markday275/RoboCup/CAD/InductiveProxSensor.SLDPRT

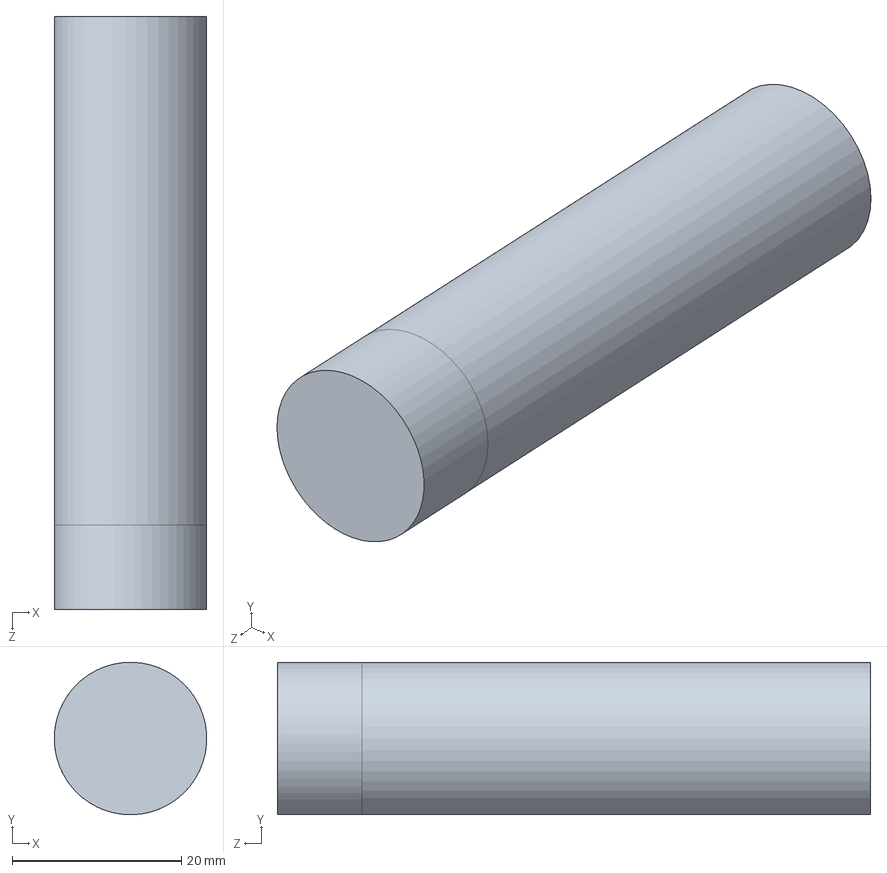
[picture p46: CAD file, 2024-11-14]
CAD/InductiveProxSensor.SLDPRT
18.0 x 18.0 x 70.0 mm
