markday275/RoboCup/CAD/Gate.SLDPRT

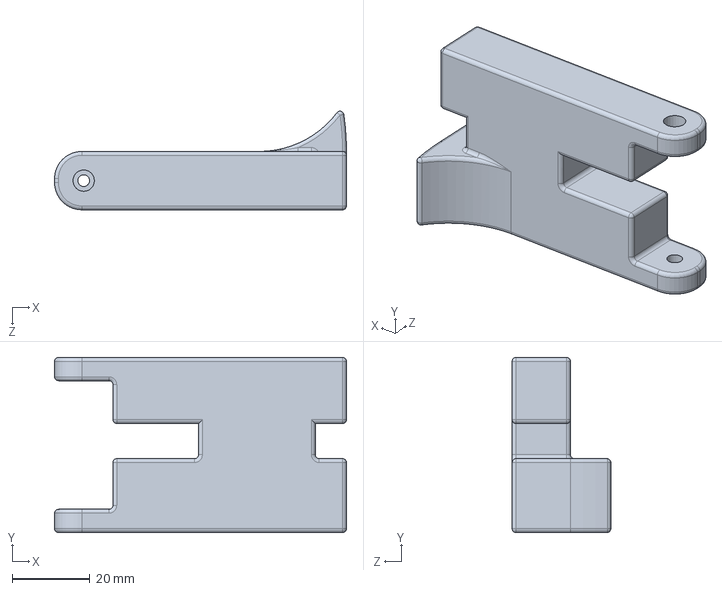
[picture p47: CAD file, 2024-11-14]
CAD/Gate.SLDPRT
75.0 x 45.0 x 25.3 mm
