markday275/RoboCup/CAD/RH Tray Back.SLDPRT

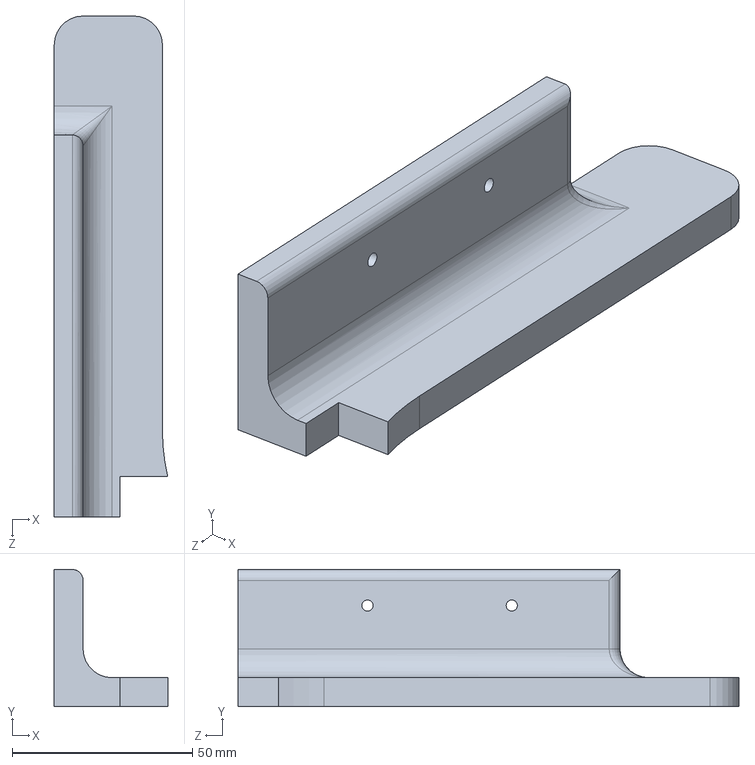
[picture p48: CAD file, 2024-11-14]
CAD/RH Tray Back.SLDPRT
31.5 x 38.0 x 138.9 mm
