markday275/RoboCup/CAD/RH Tray Front.SLDPRT

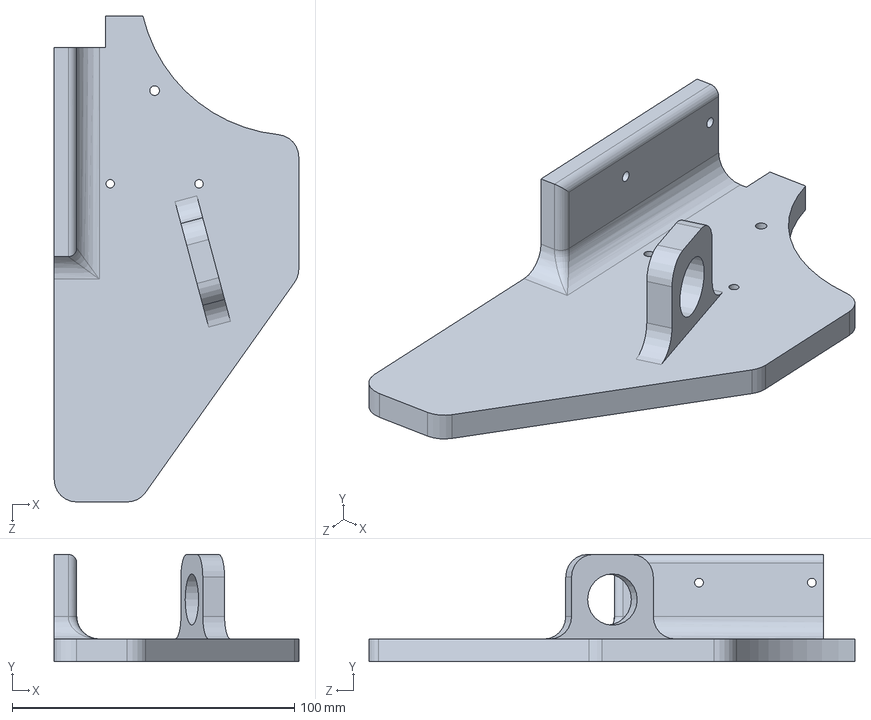
[picture p49: CAD file, 2024-11-14]
CAD/RH Tray Front.SLDPRT
86.8 x 38.0 x 172.3 mm
