markday275/RoboCup/CAD/digitalBoardBracket.SLDPRT

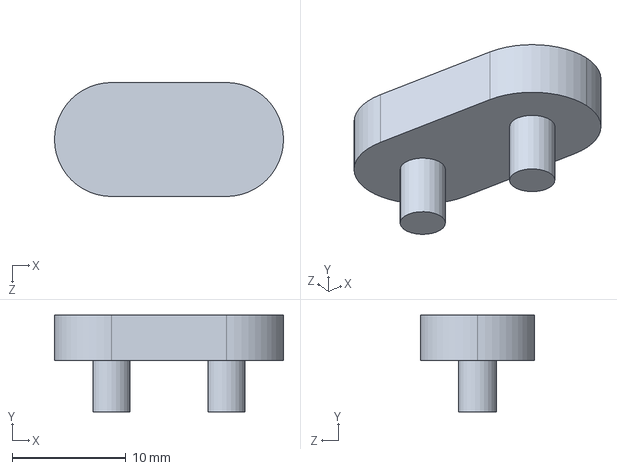
[picture p50: CAD file, 2024-11-14]
CAD/digitalBoardBracket.SLDPRT
20.1 x 8.50 x 10.0 mm
