markday275/RoboCup/CAD/ColourSensor.SLDPRT

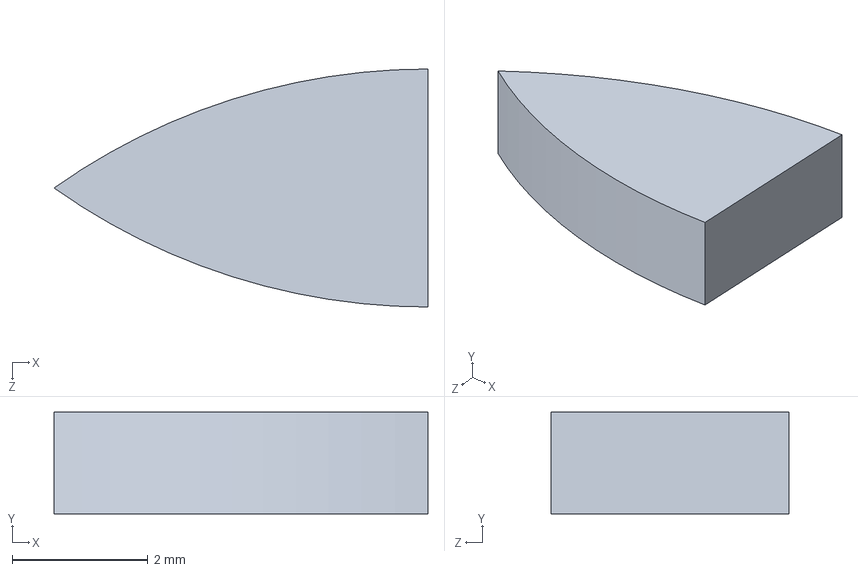
[picture p51: CAD file, 2024-11-14]
CAD/ColourSensor.SLDPRT
5.50 x 1.50 x 3.50 mm
