markday275/RoboCup/CAD/Partition.SLDPRT

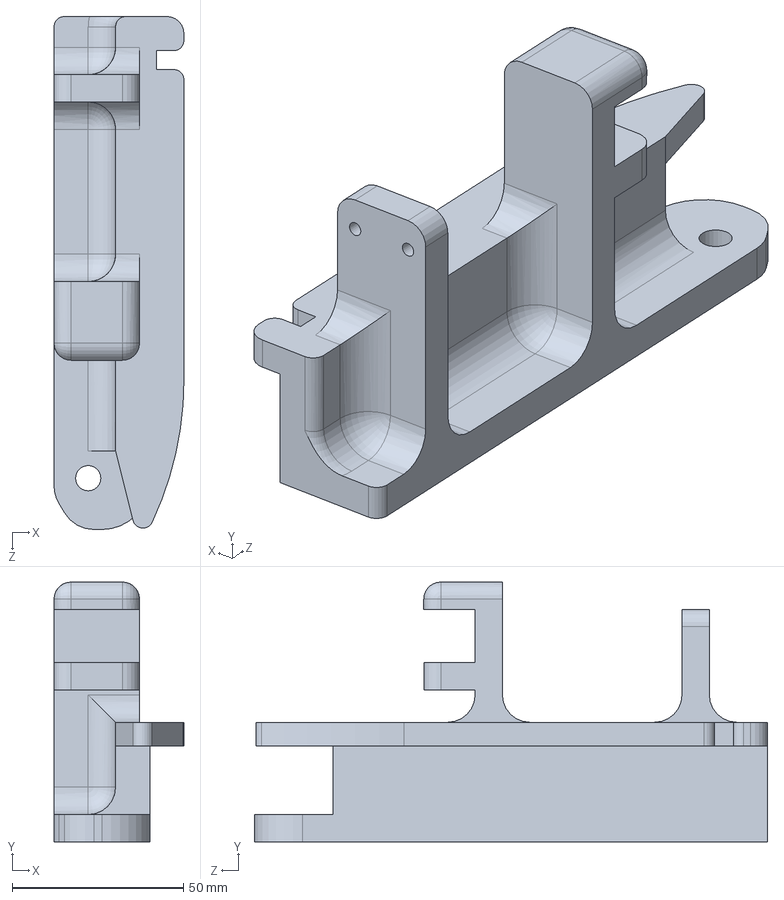
[picture p52: CAD file, 2024-11-14]
CAD/Partition.SLDPRT
38.0 x 76.0 x 150.0 mm
