markday275/RoboCup/CAD/digitalBoardBracket2.SLDPRT

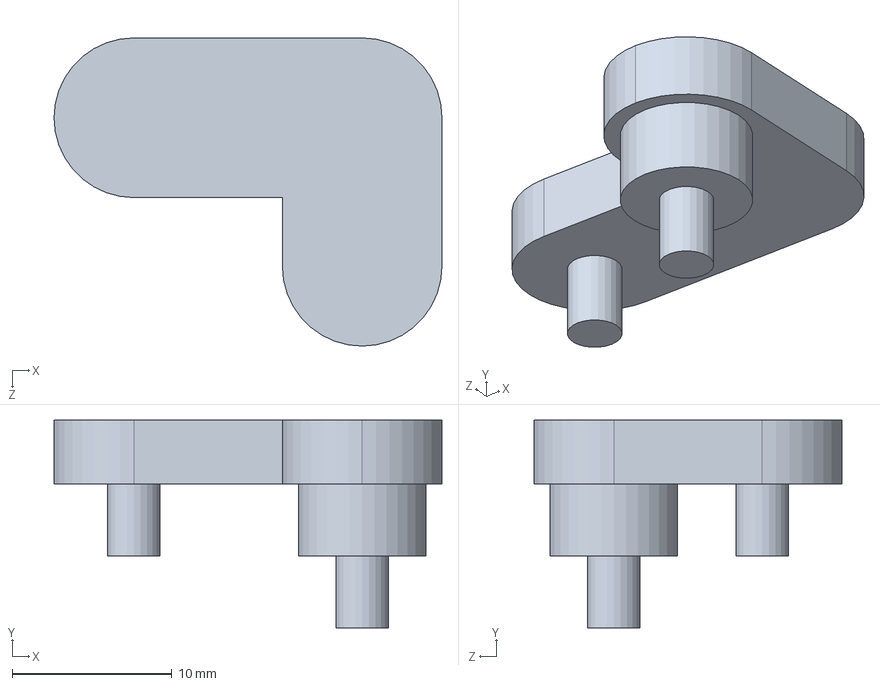
[picture p53: CAD file, 2024-11-14]
CAD/digitalBoardBracket2.SLDPRT
24.3 x 13.0 x 19.3 mm
