markday275/RoboCup/CAD/inductiveBoardBracket.SLDPRT

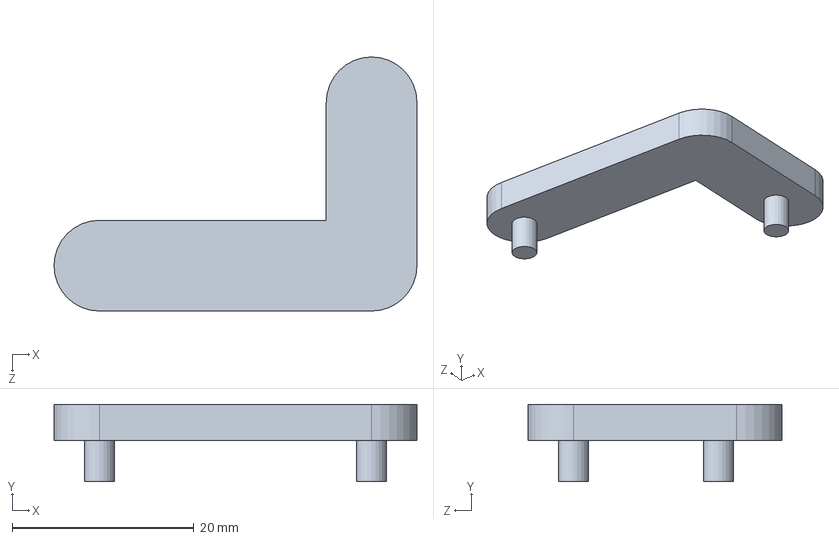
[picture p54: CAD file, 2024-11-14]
CAD/inductiveBoardBracket.SLDPRT
40.0 x 8.50 x 28.0 mm
