markday275/RoboCup/CAD/RH TRAY.SLDPRT

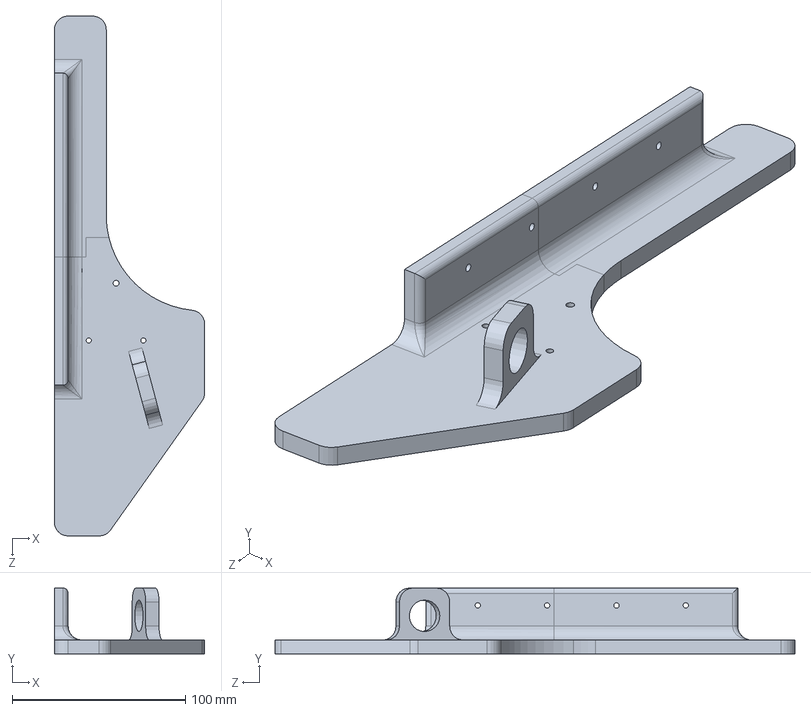
[picture p55: CAD file, 2024-11-14]
CAD/RH TRAY.SLDPRT
86.8 x 38.0 x 300.0 mm
