markday275/RoboCup/CAD/LH TRAY NEW SLOT.SLDPRT

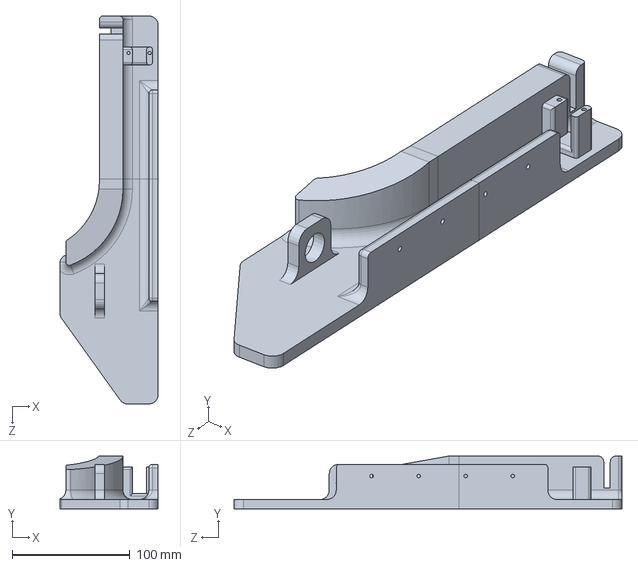
[picture p56: CAD file, 2024-11-14]
CAD/LH TRAY NEW SLOT.SLDPRT
83.8 x 45.0 x 330.0 mm
