markday275/RoboCup/CAD/LH TRAY.SLDPRT

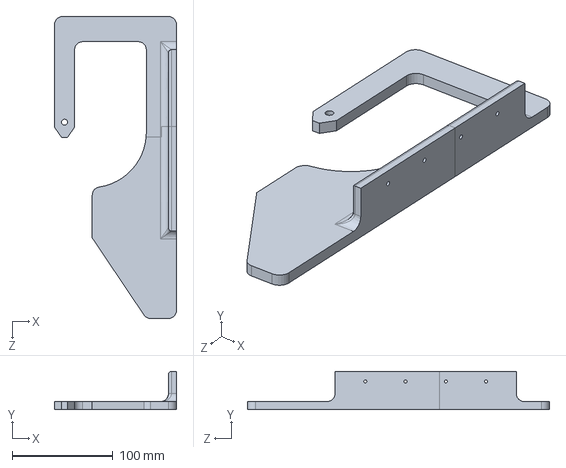
[picture p57: CAD file, 2024-11-14]
CAD/LH TRAY.SLDPRT
121.2 x 38.0 x 300.0 mm
