markday275/RoboCup/CAD/Digital_IR_Sensor.SLDPRT

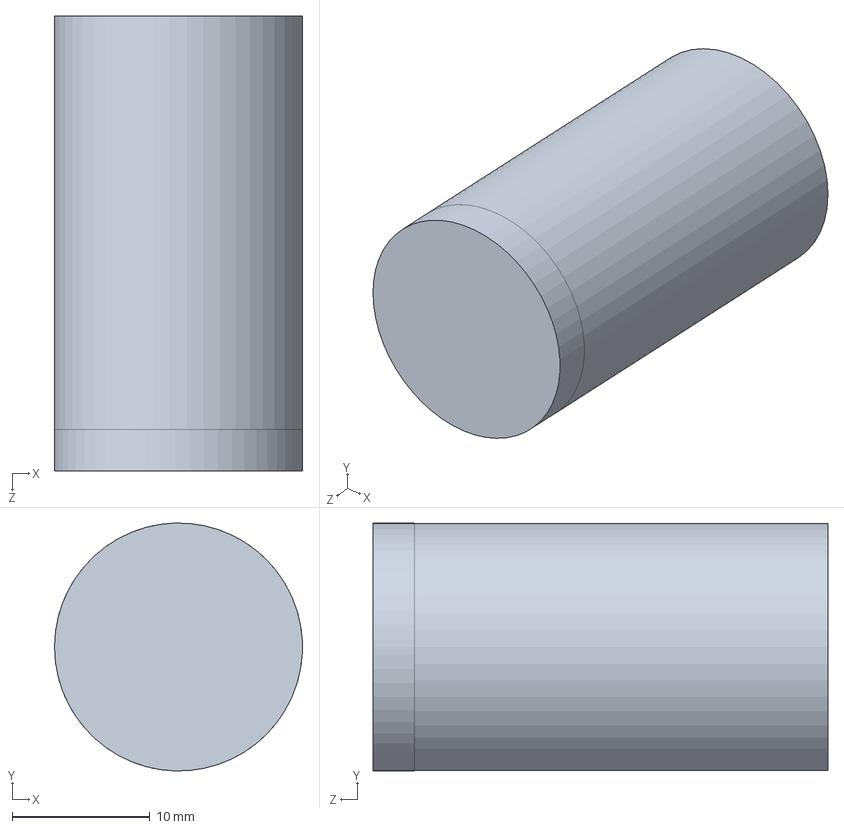
[picture p58: CAD file, 2024-11-14]
CAD/Digital_IR_Sensor.SLDPRT
18.0 x 18.0 x 33.0 mm
