markday275/RoboCup/CAD/WireChannelVert.SLDPRT

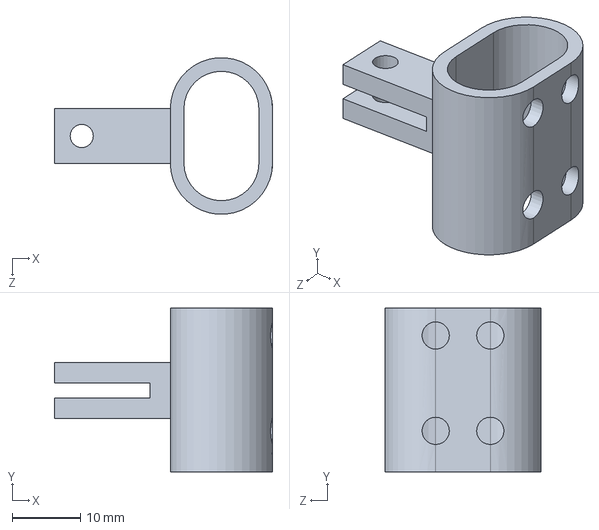
[picture p59: CAD file, 2024-11-14]
CAD/WireChannelVert.SLDPRT
32.0 x 24.0 x 22.9 mm
