markday275/RoboCup/CODE/finite_state_machine.h

/************************************
 *        finite_state_machine.h       *
 * 
 * Finite State Machine Header
 * 
 * Arthors 
 *        Mark   Day
 *        Jack   Wilson
 *        Kieran James
 *************************************/

#ifndef FINITE_STATE_MACHINE_H_
#define FINITE_STATE_MACHINE_H_


#define START_BUTTON 26


/*
* MAIN FUNCTION
*
* Runs the State machine
*/ 
void runStateMachine(void);


#endif /* FINITE_STATE_MACHINE_H_ */
